TimGoll/pcb_buck_test/benchmarks/data/tps_neg_in_10.0.csv

I_out | U_out | I_in | U_in
0 | -4.95 | 0 | 10.00
50 | -4.93 | 31 | 10.00
100 | -4.93 | 64 | 10.00
150 | -4.92 | 97 | 10.00
200 | -4.92 | 129 | 10.00
250 | -4.92 | 158 | 10.00
300 | -4.92 | 188 | 10.00
350 | -4.92 | 219 | 10.00
400 | -4.92 | 251 | 10.00
450 | -4.92 | 283 | 10.00
500 | -4.92 | 318 | 10.00
550 | -4.92 | 351 | 10.00
600 | -4.92 | 387 | 10.00
650 | -4.92 | 425 | 10.00
700 | -4.91 | 464 | 10.00
750 | -4.91 | 507 | 10.00
800 | -4.91 | 551 | 10.00
850 | -4.91 | 603 | 10.00
900 | -4.69 | 619 | 10.00
950 | -4.13 | 580 | 10.00
