TimGoll/pcb_buck_test/benchmarks/data/tps_neg_in_5.0.csv

I_out | U_out | I_in | U_in
0 | -4.95 | 0 | 5.00
50 | -4.95 | 65 | 5.00
100 | -4.93 | 133 | 5.00
150 | -4.93 | 194 | 5.00
200 | -4.93 | 263 | 5.00
250 | -4.93 | 335 | 5.00
300 | -4.93 | 421 | 5.00
350 | -4.93 | 516 | 5.00
400 | -4.92 | 628 | 5.00
450 | -4.92 | 801 | 5.00
500 | -4.56 | 976 | 5.00
550 | -3.98 | 931 | 5.00
600 | -3.51 | 890 | 5.00
