TimGoll/pcb_buck_test/benchmarks/data/tps_neg_in_5.5.csv

I_out | U_out | I_in | U_in
0 | -4.95 | 0 | 5.50
50 | -4.95 | 59 | 5.50
100 | -4.93 | 120 | 5.50
150 | -4.93 | 176 | 5.50
200 | -4.93 | 235 | 5.50
250 | -4.93 | 297 | 5.50
300 | -4.93 | 367 | 5.50
350 | -4.93 | 444 | 5.50
400 | -4.93 | 531 | 5.50
450 | -4.92 | 632 | 5.50
500 | -4.92 | 762 | 5.50
550 | -4.77 | 926 | 5.50
600 | -4.18 | 885 | 5.50
